Proxmark/proxmark3/pcb/proxmark3_fix/IN2_layer_preview.png

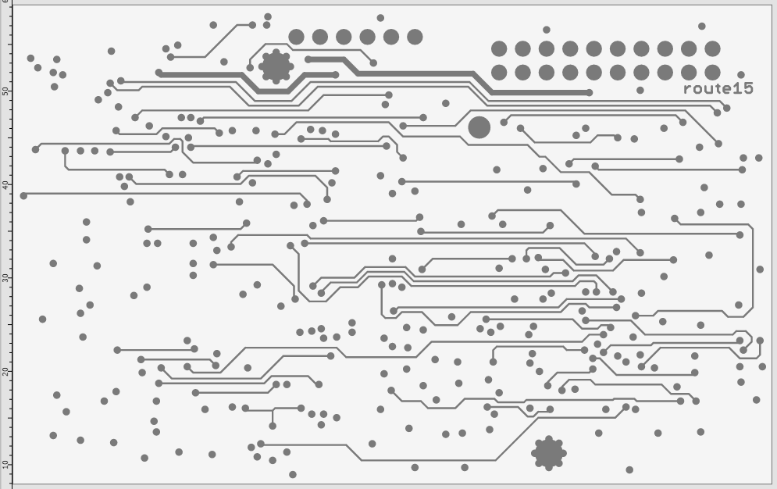
pcb/proxmark3_fix/IN2_layer_preview.png
