Proxmark/proxmark3/pcb/proxmark3_fix/TOP_layer_preview.png

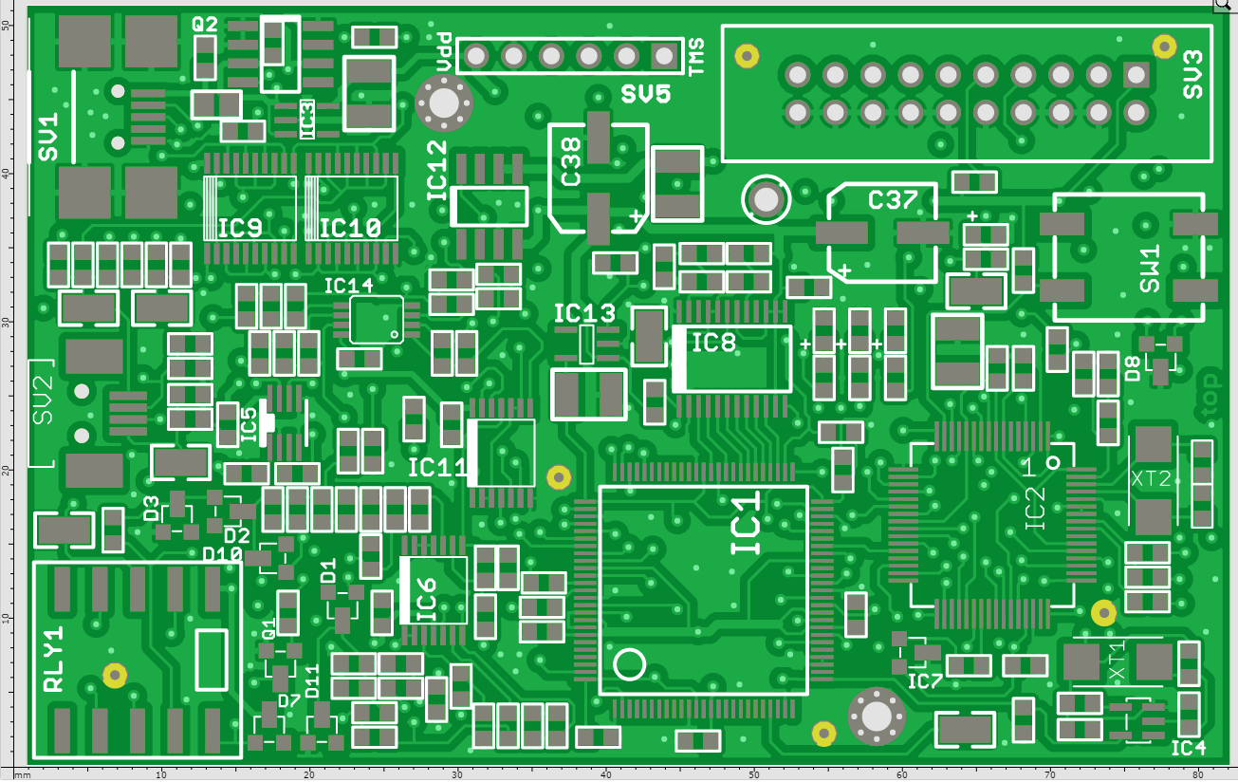
pcb/proxmark3_fix/TOP_layer_preview.png
